uk-r2-builders-club/droid_driving_course/static/cropped-BDround512-150x150.jpg

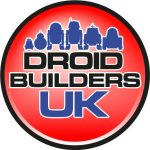
static/cropped-BDround512-150x150.jpg
