uk-r2-builders-club/droid_driving_course/static/images/toprun/1.gif

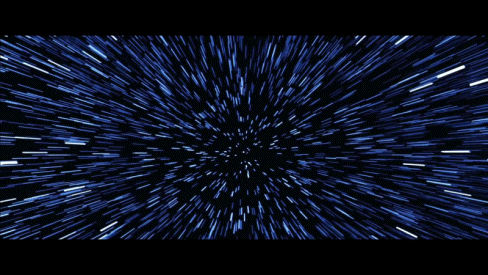
static/images/toprun/1.gif
