uk-r2-builders-club/droid_driving_course/static/images/toprun/3.gif

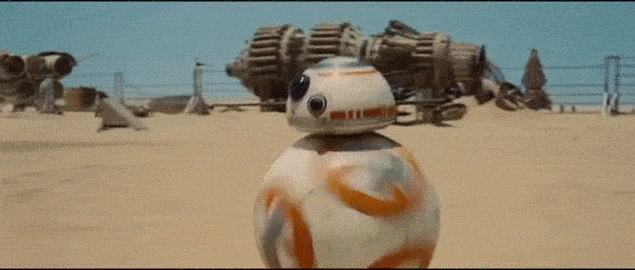
static/images/toprun/3.gif
