uk-r2-builders-club/droid_driving_course/tools/rfid/mifare_dump.py

#!/usr/bin/python3
# Example of detecting and reading a block from a MiFare NFC card.
# Author: Tony DiCola & Roberto Laricchia
# Copyright (c) 2015 Adafruit Industries
#
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
"""
This example shows connecting to the PN532 and writing & reading an ntag2xx
type RFID tag
"""

import board
import busio
import binascii
import sys
import ndef
import requests
import serial
from digitalio import DigitalInOut
from adafruit_pn532.spi import PN532_SPI

# I2C connection:
#i2c = busio.I2C(board.SCL, board.SDA)

# Non-hardware reset/request with I2C
#pn532 = PN532_I2C(i2c, debug=False)

spi = busio.SPI(board.SCK, board.MOSI, board.MISO)
cs_pin = DigitalInOut(board.D8)
pn532 = PN532_SPI(spi, cs_pin, debug=False)

ic, ver, rev, support = pn532.get_firmware_version()
print('Found PN532 with firmware version: {0}.{1}'.format(ver, rev))

# Configure PN532 to communicate with MiFare cards
pn532.SAM_configuration()

keym = bytes([ 0xA0, 0xA1, 0xA2, 0xA3, 0xA4, 0xA5 ])
keya = bytes([ 0xD3, 0xF7, 0xD3, 0xF7, 0xD3, 0xF7 ])
baseurl = "http://localhost:5000/"

print('Waiting for RFID/NFC card to write to!')
while True:
    # Check if a card is available to read
    uid = pn532.read_passive_target(timeout=0.1)
    # Try again if no card is available.
    if uid is None:
        continue

    print('Found card with UID:', [hex(i) for i in uid])

    # Authenticate block
    pn532.mifare_classic_authenticate_block(uid, 4, 0x60, keya)

    block = bytearray()
    for x in range(4,63):
        if (x+1)%4==0:
            pn532.mifare_classic_authenticate_block(uid, x+1, 0x60, keya)
        else: 
            data = pn532.mifare_classic_read_block(x)
            print("Data: 0x{0}".format(binascii.hexlify(data)))
            block.extend(data)

    start = 0
    end = 0

    for x in range(0, 20):
        if block[x] == 0x03:
           print("Start of ndef: ", x)
           start = x + 2
           length = int(block[x+1])
           print("Length: ", length)
           end = x + length + 2
           print("End of ndef: ", end)
        else: 
           print("Searching for start of ndef block: ",block[x])

    print('All: 0x{0}'.format(binascii.hexlify(block[start:end])))

    decoder = ndef.message_decoder(block[start:end])
    for x in decoder:
        print("Data: {0}".format(x.data))
